danpeirce/scad-keyboard-cases/crkbd/crkbd-case-bottom-of-top.png

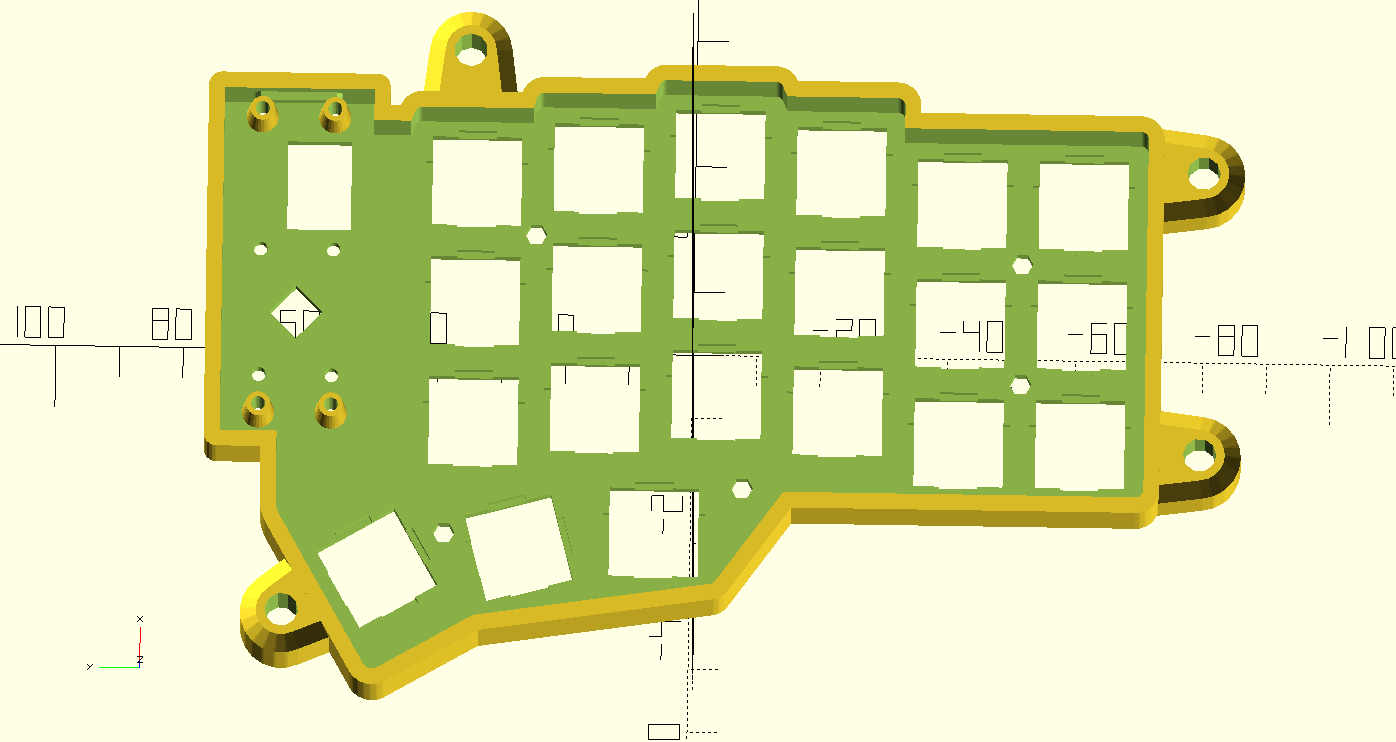
crkbd/crkbd-case-bottom-of-top.png
