danpeirce/scad-keyboard-cases/crkbd/crkbd-case-top-of-top.png

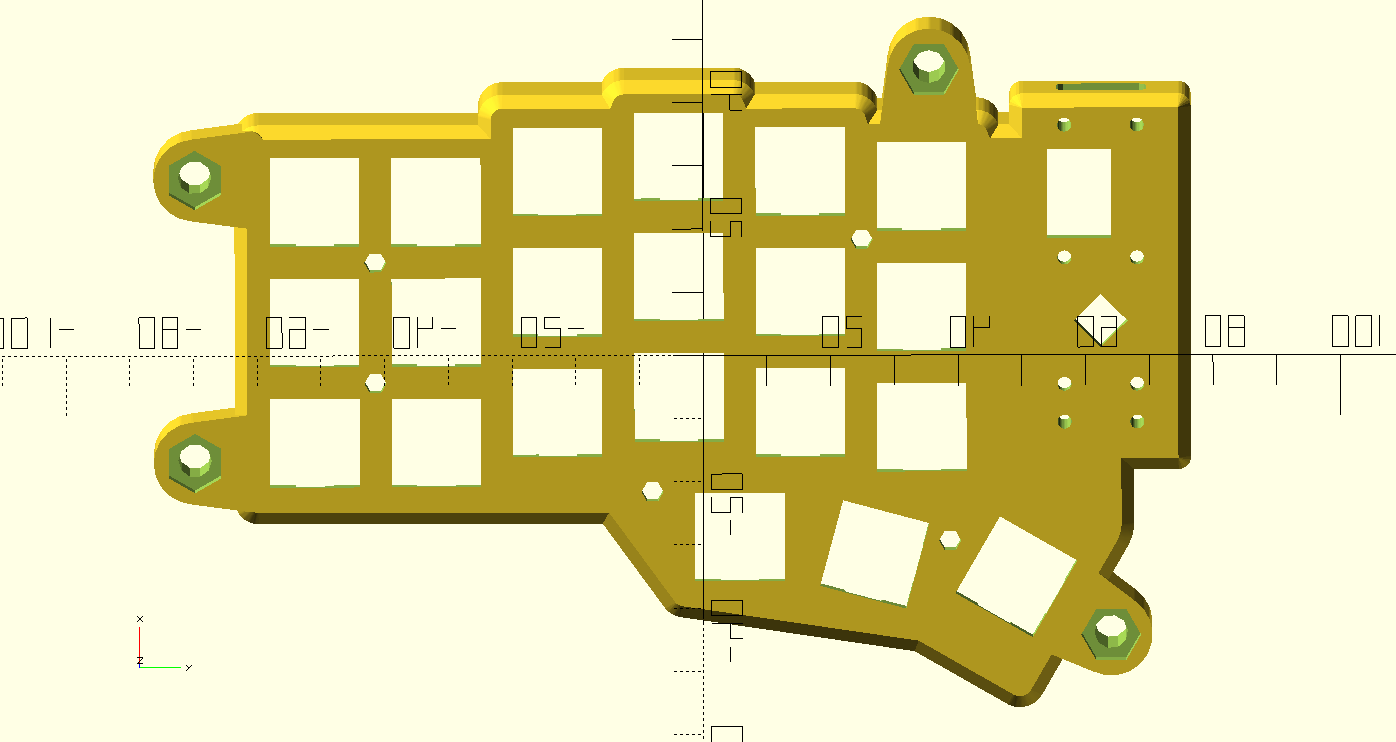
crkbd/crkbd-case-top-of-top.png
