danpeirce/scad-keyboard-cases/crkbd/pico-dim.png

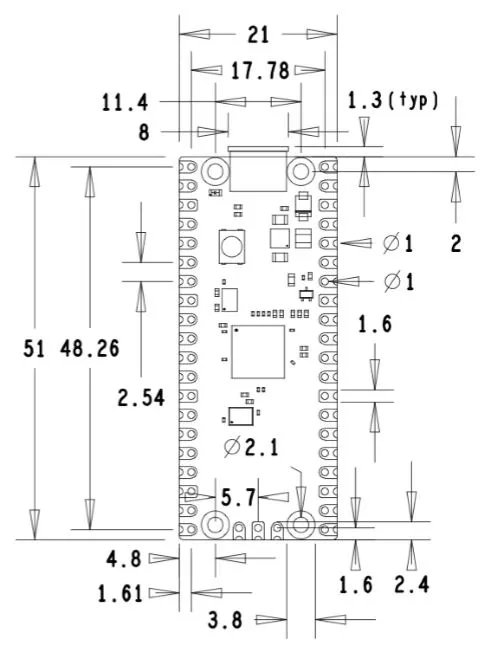
crkbd/pico-dim.png
