danpeirce/scad-keyboard-cases/crkbd/pico.scad

module pico() { translate([ 0, 0, 1 ]) rotate(a = [ 90, 0, 90 ]) import("RaspberryPiPico.amf", convexity = 3); }

module pico_test() { pico(); }

//pico_test();
