danpeirce/scad-keyboard-cases/crkbd/orig/crkbd-mods.scad

svg_scale=0.755;

union() {
    import("C:/Users/danp/Documents/Ender/scad-keyboard-cases/crkbd/orig/crkbd-left-bottom.svg");
    translate([162, 38]) square([22/svg_scale, 53/svg_scale], center=false);
}
